timothy-joseph/timotelemetry_timounu/Software/dat_software/components/lora_driver/lora_driver_config.h

/*
 * File containing the configuration for the lora driver:
 * - thread stack sizes
 * - length of the commands queue
 * - rx and tx pins
 */
#ifndef LORA_DRIVER_CONFIG_H
#define LORA_DRIVER_CONFIG_H

#endif
